CarlosValadao/Entelechy/Entelechy/Entelechy_3D/BH-26.STEP

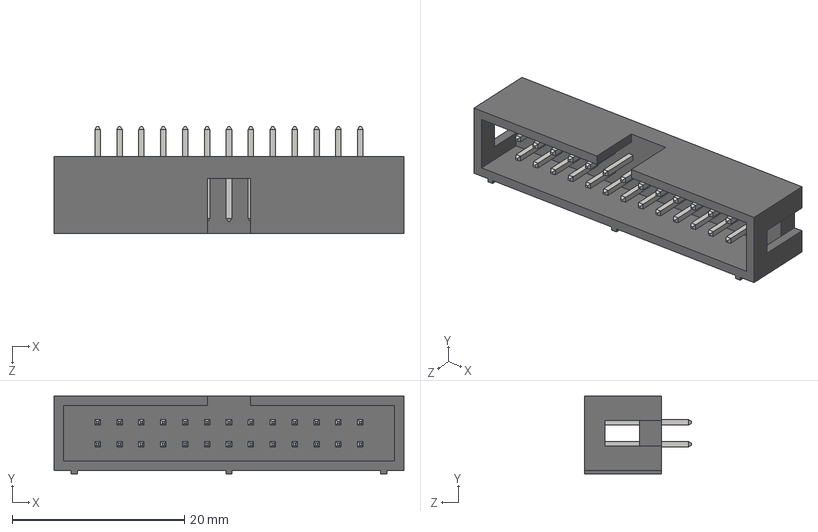
[picture p41: CAD file, 2026-02-17]
Entelechy/Entelechy_3D/BH-26.STEP
40.6 x 9.00 x 12.4 mm
