CarlosValadao/Entelechy/Entelechy/Entelechy_3D/BH-34.STEP

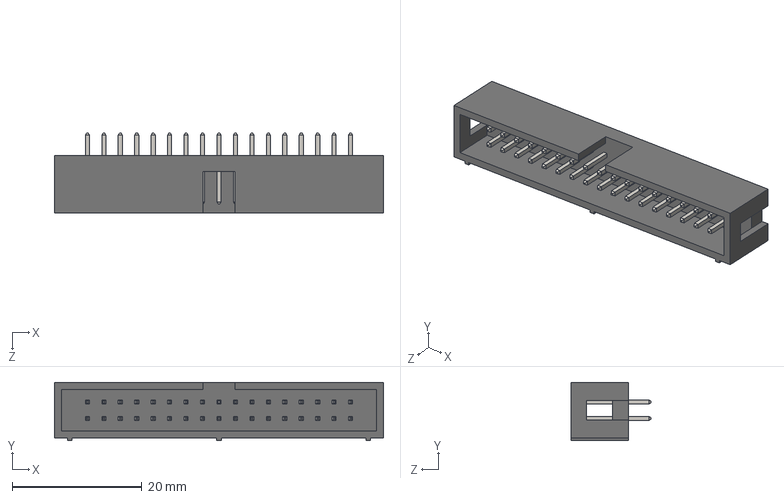
[picture p42: CAD file, 2026-02-17]
Entelechy/Entelechy_3D/BH-34.STEP
50.8 x 9.00 x 12.4 mm
