CarlosValadao/Entelechy/Entelechy/Entelechy_3D/BH-14R.STEP

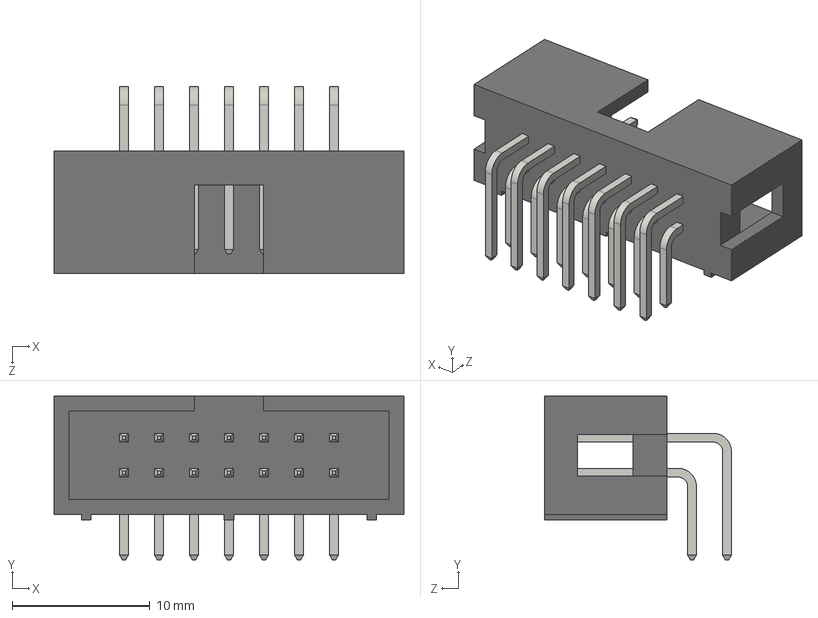
[picture p43: CAD file, 2026-02-17]
Entelechy/Entelechy_3D/BH-14R.STEP
25.4 x 11.9 x 13.6 mm
