CarlosValadao/Entelechy/Entelechy/Entelechy_3D/BH-60R.STEP

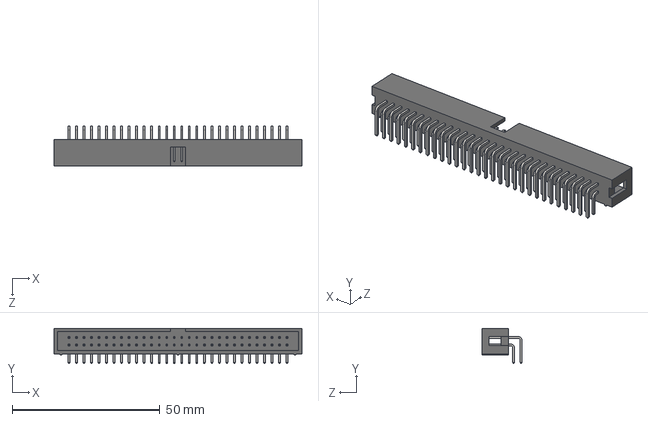
[picture p44: CAD file, 2026-02-17]
Entelechy/Entelechy_3D/BH-60R.STEP
83.8 x 11.9 x 13.6 mm
