CarlosValadao/Entelechy/Entelechy/Entelechy_3D/BH-64R.STEP

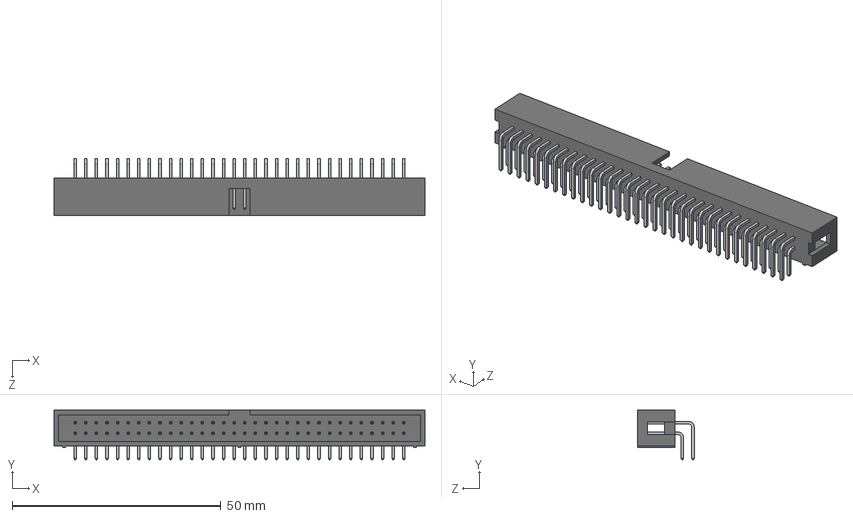
[picture p45: CAD file, 2026-02-17]
Entelechy/Entelechy_3D/BH-64R.STEP
88.9 x 11.9 x 13.6 mm
