CarlosValadao/Entelechy/Entelechy/Entelechy_3D/BH-12.STEP

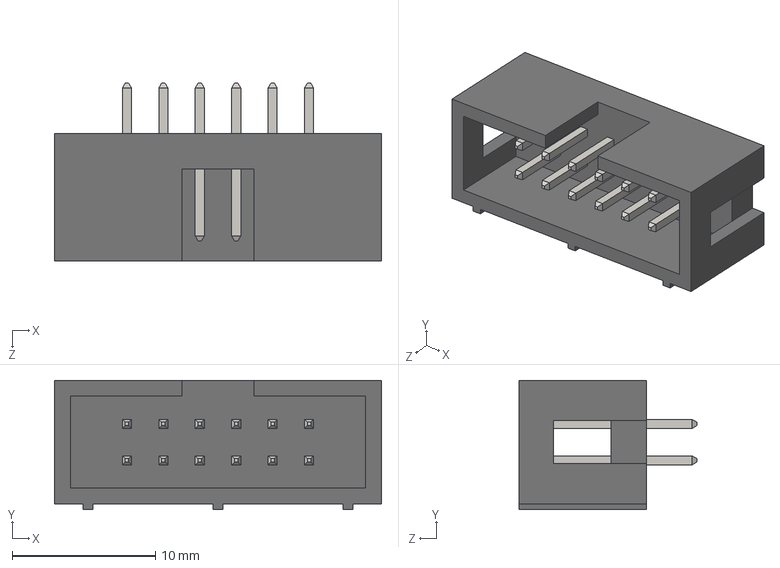
[picture p46: CAD file, 2026-02-17]
Entelechy/Entelechy_3D/BH-12.STEP
22.8 x 9.00 x 12.4 mm
