CarlosValadao/Entelechy/Entelechy/Entelechy_3D/LED7seg036.stp

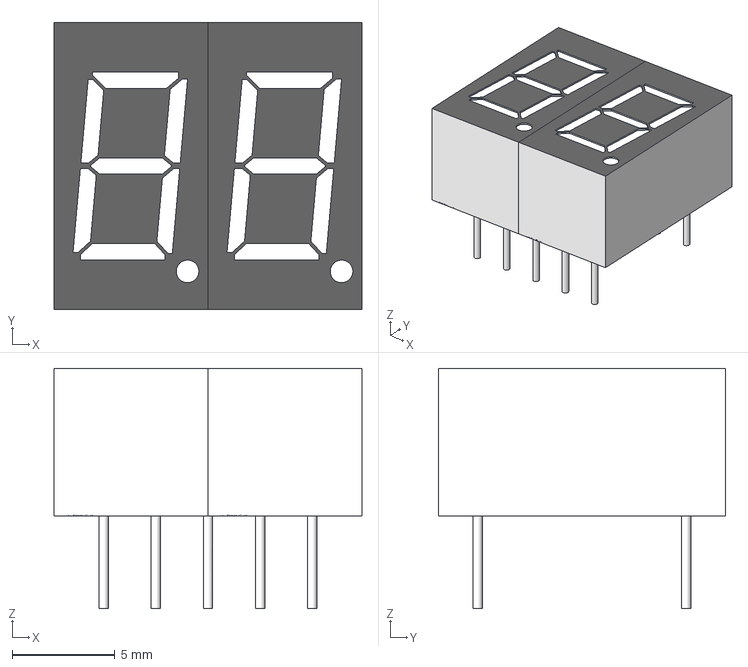
[picture p47: CAD file, 2026-02-17]
Entelechy/Entelechy_3D/LED7seg036.stp
15.0 x 14.0 x 11.7 mm
