CarlosValadao/Entelechy/Entelechy/Entelechy_3D/BH-26R.STEP

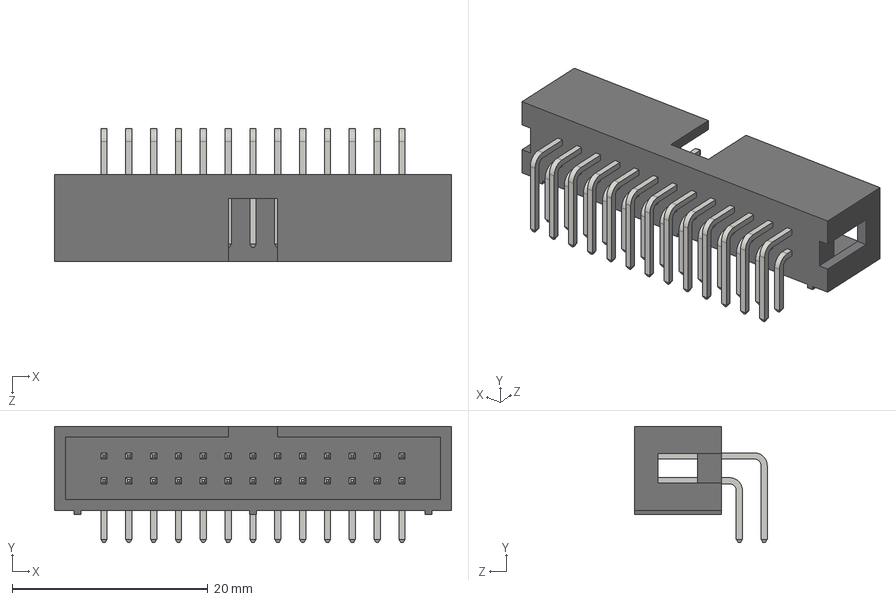
[picture p48: CAD file, 2026-02-17]
Entelechy/Entelechy_3D/BH-26R.STEP
40.6 x 11.9 x 13.6 mm
