CarlosValadao/Entelechy/Entelechy/Entelechy_3D/BH-34R.STEP

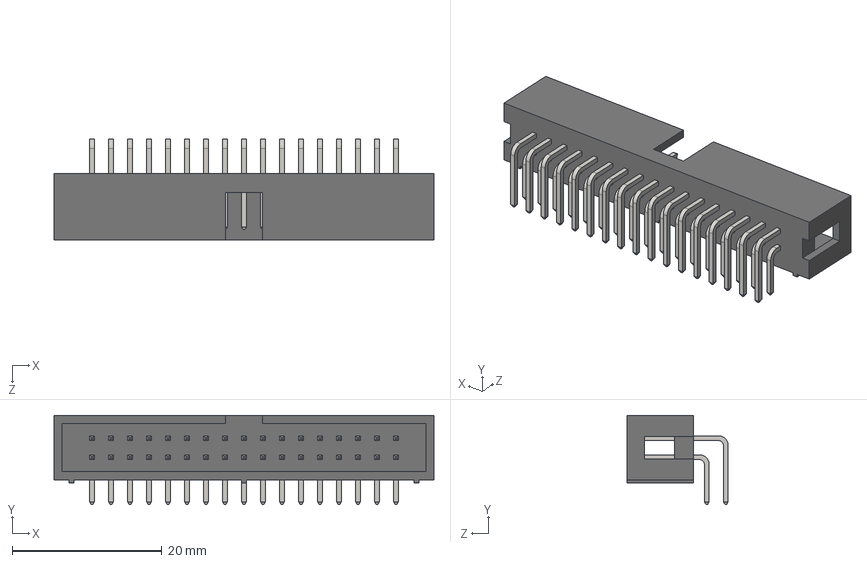
[picture p49: CAD file, 2026-02-17]
Entelechy/Entelechy_3D/BH-34R.STEP
50.8 x 11.9 x 13.6 mm
