CarlosValadao/Entelechy/Entelechy/Entelechy_3D/BH-20R.STEP

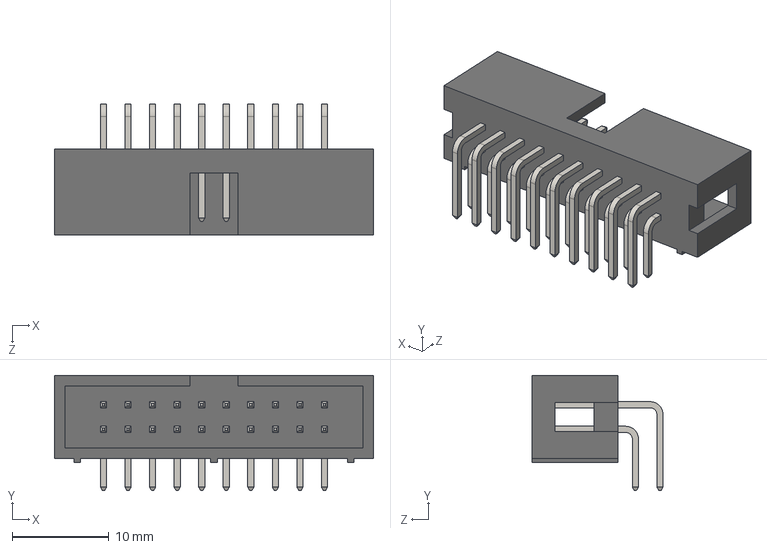
[picture p50: CAD file, 2026-02-17]
Entelechy/Entelechy_3D/BH-20R.STEP
33.0 x 11.9 x 13.6 mm
