CarlosValadao/Entelechy/Entelechy/Entelechy_3D/BH-14.STEP

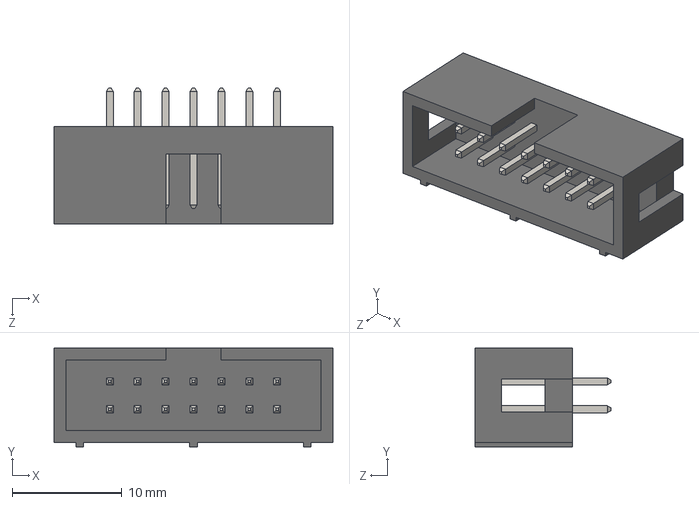
[picture p51: CAD file, 2026-02-17]
Entelechy/Entelechy_3D/BH-14.STEP
25.4 x 9.00 x 12.4 mm
