CarlosValadao/Entelechy/Entelechy/Entelechy_3D/BH-10R.STEP

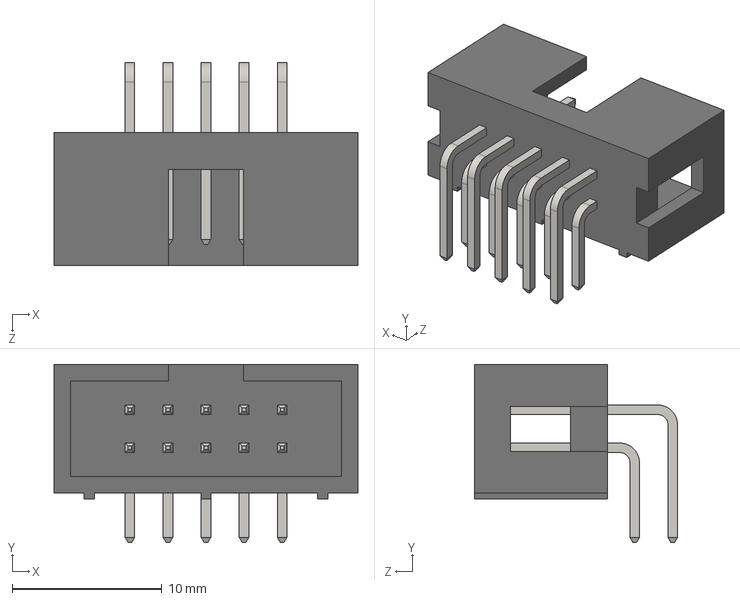
[picture p52: CAD file, 2026-02-17]
Entelechy/Entelechy_3D/BH-10R.STEP
20.3 x 11.9 x 13.6 mm
