CarlosValadao/Entelechy/Entelechy/Entelechy_3D/WSL 6W IDC Bh Connector 6-Pin v3.step

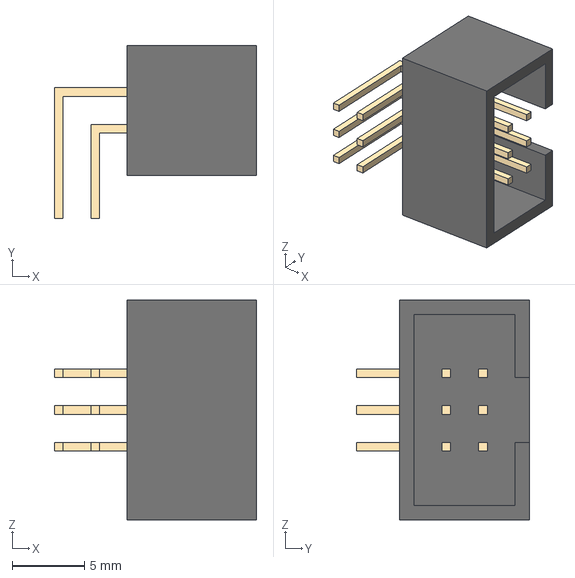
[picture p53: CAD file, 2026-02-17]
Entelechy/Entelechy_3D/WSL 6W IDC Bh Connector 6-Pin v3.step
14.0 x 12.0 x 15.2 mm
Pins
Case
