CarlosValadao/Entelechy/Entelechy/Entelechy_3D/BH-40R.STEP

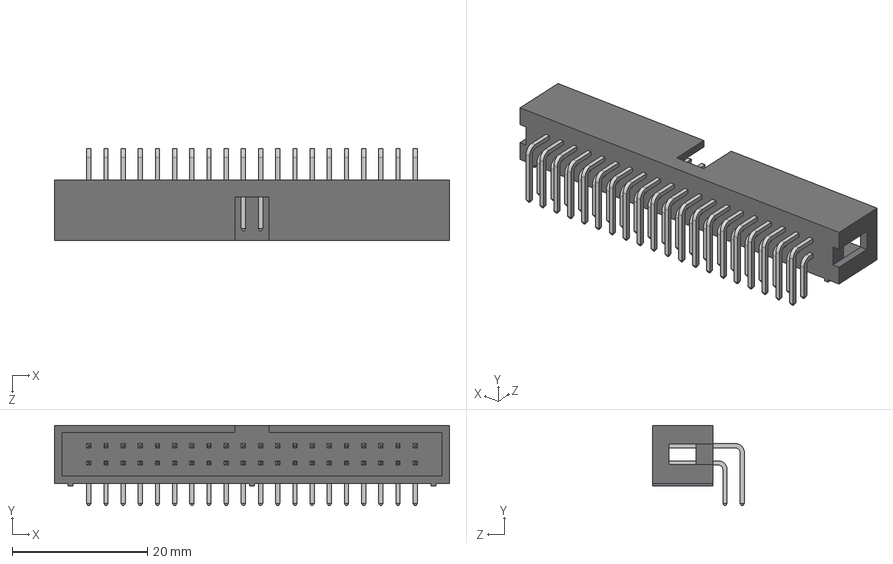
[picture p54: CAD file, 2026-02-17]
Entelechy/Entelechy_3D/BH-40R.STEP
58.4 x 11.9 x 13.6 mm
