CarlosValadao/Entelechy/Entelechy/Entelechy_3D/BH-12R.STEP

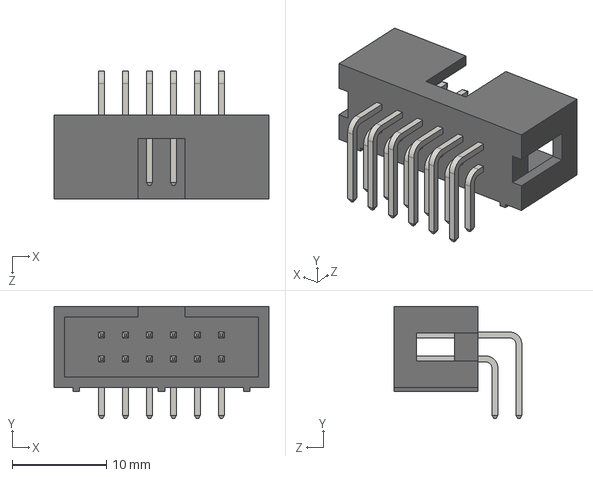
[picture p55: CAD file, 2026-02-17]
Entelechy/Entelechy_3D/BH-12R.STEP
22.8 x 11.9 x 13.6 mm
