CarlosValadao/Entelechy/Entelechy/Entelechy_3D/BH-16.STEP

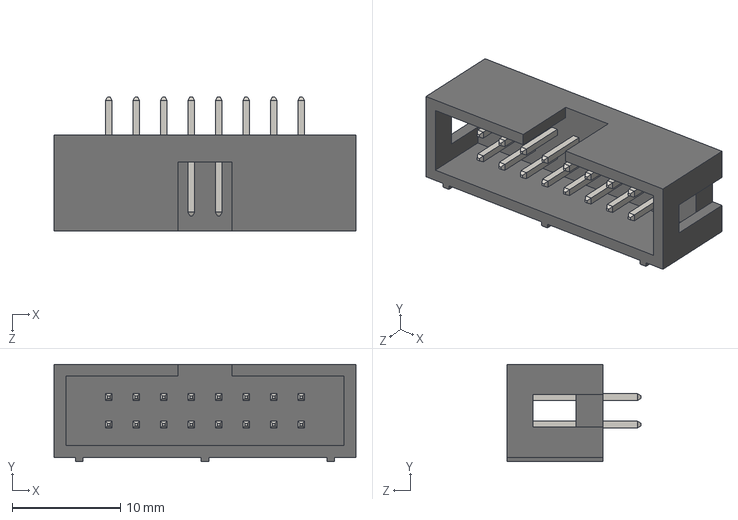
[picture p56: CAD file, 2026-02-17]
Entelechy/Entelechy_3D/BH-16.STEP
27.9 x 9.00 x 12.4 mm
