CarlosValadao/Entelechy/Entelechy/Entelechy_3D/BH-30R.STEP

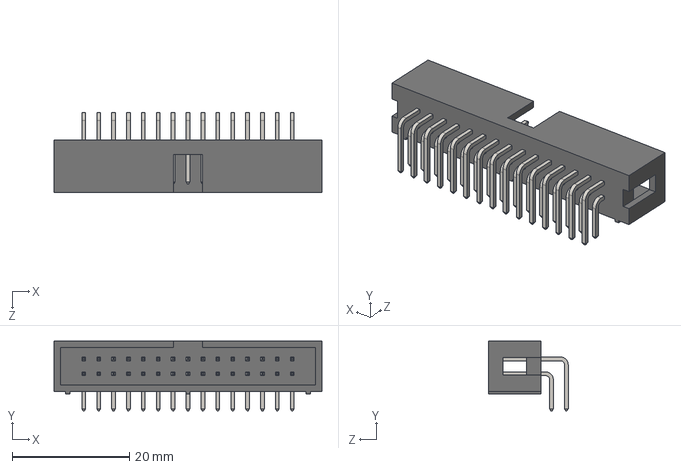
[picture p57: CAD file, 2026-02-17]
Entelechy/Entelechy_3D/BH-30R.STEP
45.7 x 11.9 x 13.6 mm
