CarlosValadao/Entelechy/Entelechy/Entelechy_3D/BH-20.STEP

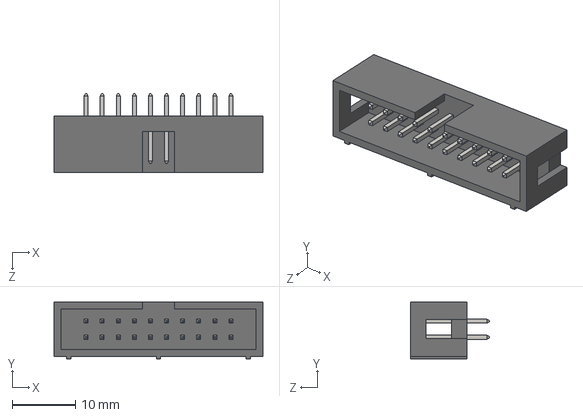
[picture p58: CAD file, 2026-02-17]
Entelechy/Entelechy_3D/BH-20.STEP
33.0 x 9.00 x 12.4 mm
