CarlosValadao/Entelechy/Entelechy/Entelechy_3D/BH-50R.STEP

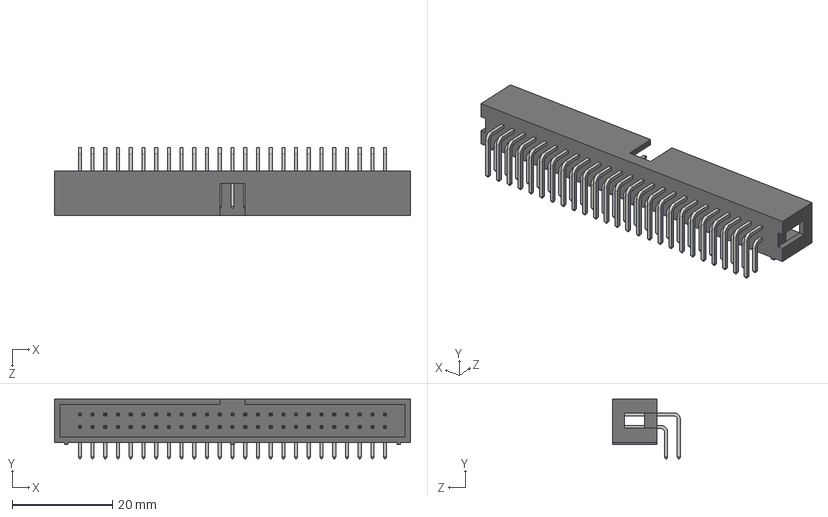
[picture p59: CAD file, 2026-02-17]
Entelechy/Entelechy_3D/BH-50R.STEP
71.1 x 11.9 x 13.6 mm
